CarmenMaria17/ProiectTSC2025/Images/image1.png

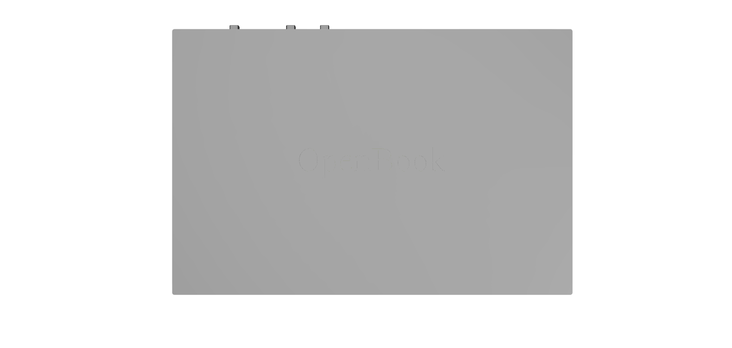
Images/image1.png
