CarmenMaria17/ProiectTSC2025/Images/image2.png

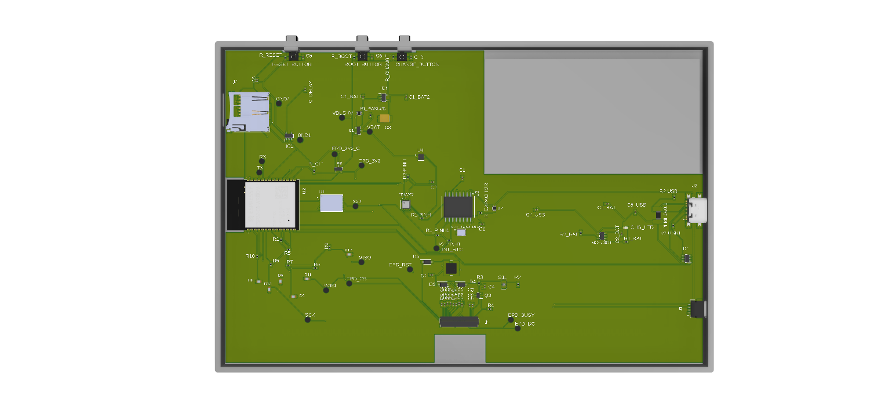
Images/image2.png
