CarmenMaria17/ProiectTSC2025/Images/image3.png

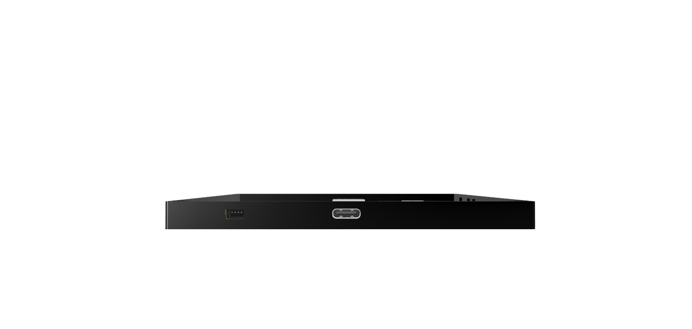
Images/image3.png
