CarmenMaria17/ProiectTSC2025/Images/image5.png

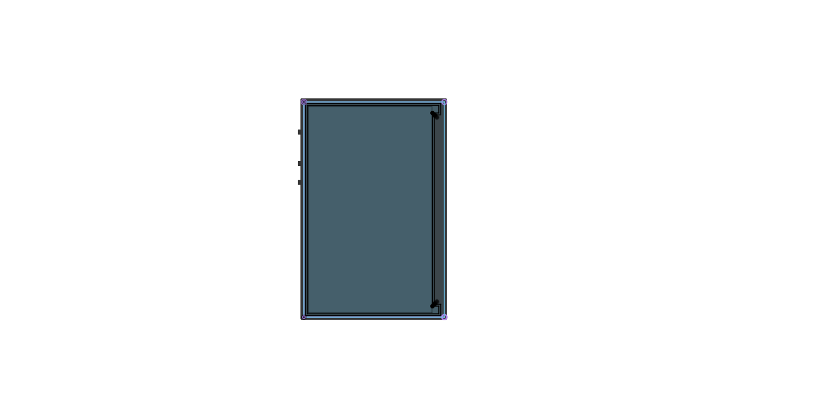
Images/image5.png
