CarmenMaria17/ProiectTSC2025/Images/image6.png

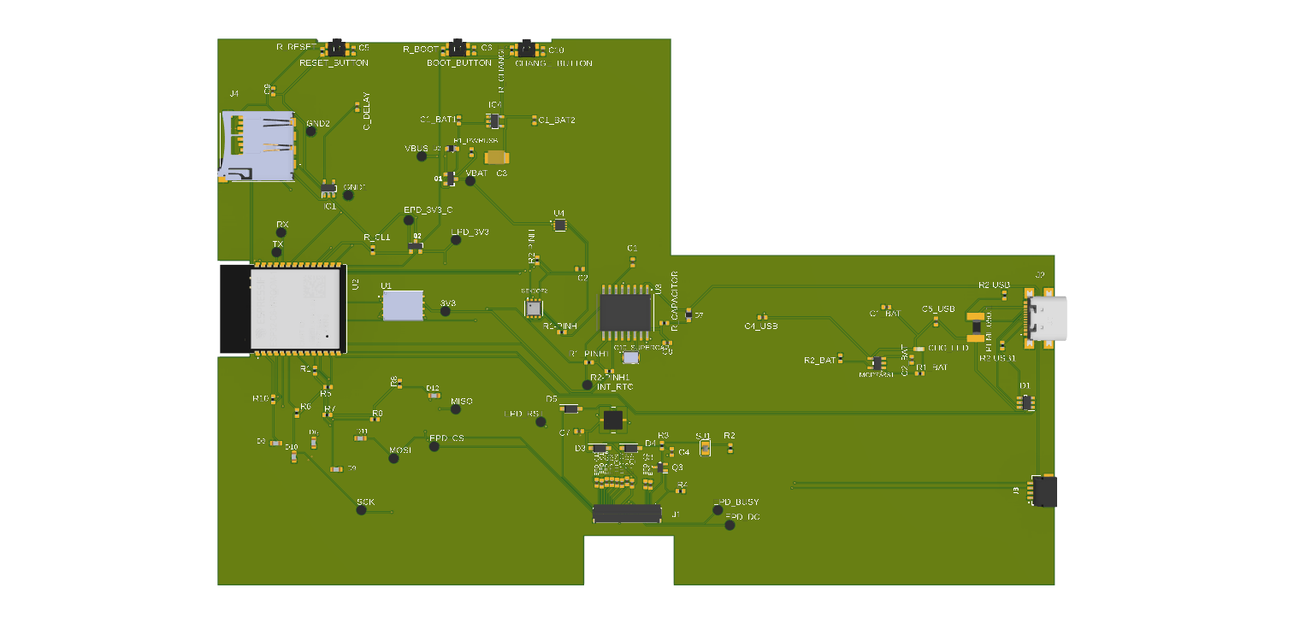
Images/image6.png
