CarmenMaria17/ProiectTSC2025/Images/image7.png

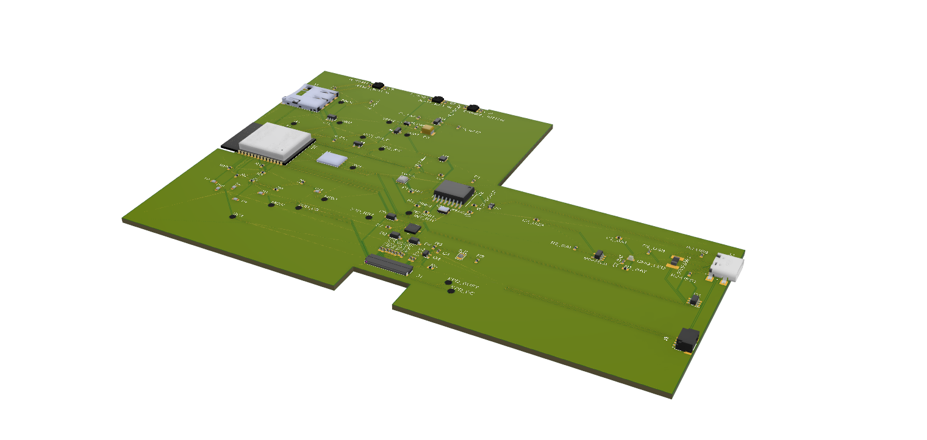
Images/image7.png
